naturalgeek/TANITA-WIFI-Retrofit/hardware/tanita_sniffer.kicad_sch

## KiCad design hardware/tanita_sniffer.kicad_sch (2026-06-14)

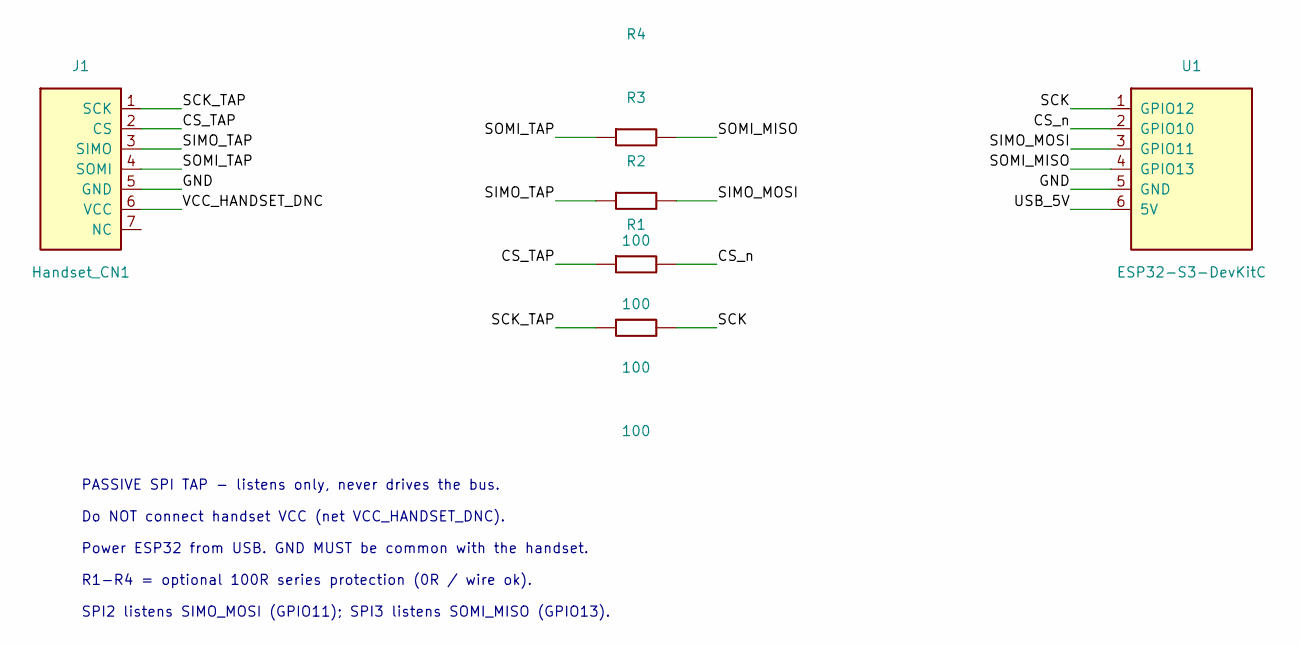
[picture p8: schematic tanita_sniffer.kicad_sch]

Parts:
J1: Handset_CN1
R1, R2, R3, R4: 100
U1: ESP32-S3-DevKitC

Connections:
CS_TAP: J1.2 (CS), R2.1
CS_n: R2.2, U1.2 (GPIO10)
GND: J1.5 (GND), U1.5 (GND)
SCK: R1.2, U1.1 (GPIO12)
SCK_TAP: J1.1 (SCK), R1.1
SIMO_MOSI: R3.2, U1.3 (GPIO11)
SIMO_TAP: J1.3 (SIMO), R3.1
SOMI_MISO: R4.2, U1.4 (GPIO13)
SOMI_TAP: J1.4 (SOMI), R4.1
USB_5V: U1.6 (5V)
VCC_HANDSET_DNC: J1.6 (VCC)

Notes on the sheet:
PASSIVE SPI TAP - listens only, never drives the bus.
Do NOT connect handset VCC (net VCC_HANDSET_DNC).
Power ESP32 from USB. GND MUST be common with the handset.
R1-R4 = optional 100R series protection (0R / wire ok).
SPI2 listens SIMO_MOSI (GPIO11); SPI3 listens SOMI_MISO (GPIO13).
