naturalgeek/TANITA-WIFI-Retrofit/photos/tanita_601_handset_pcb_top.jpeg

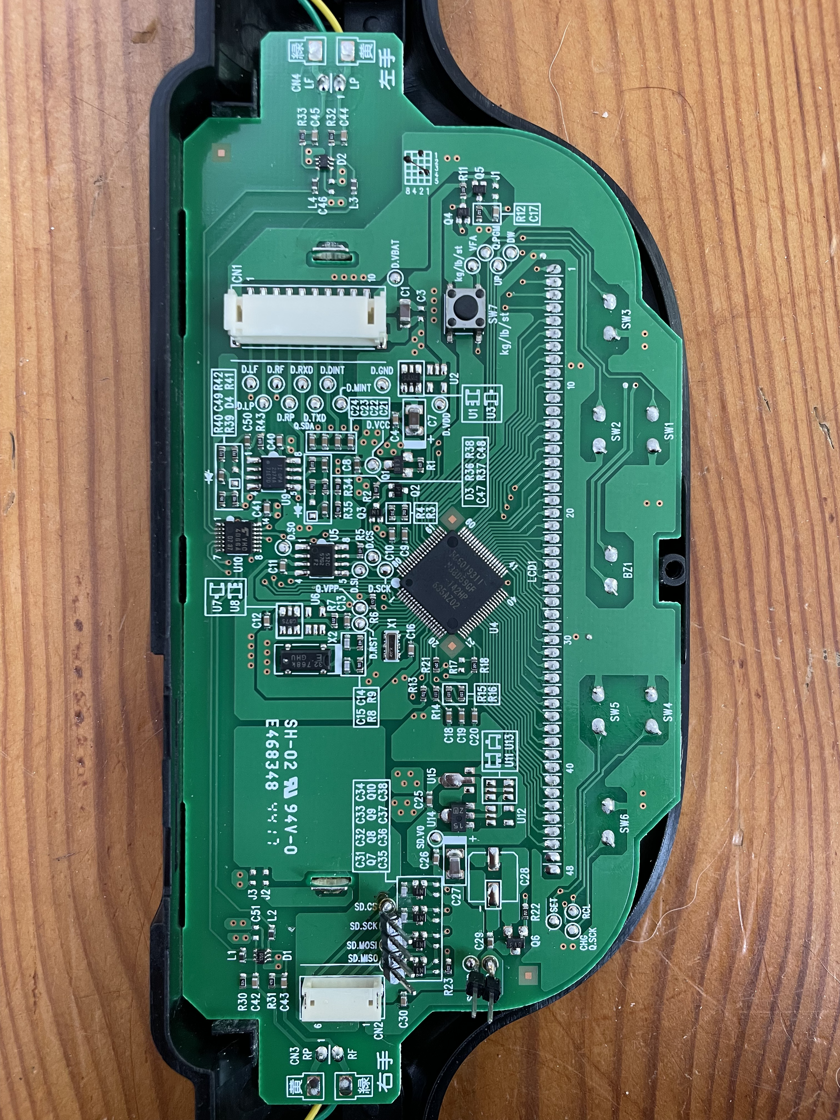
photos/tanita_601_handset_pcb_top.jpeg
